redshx86/ro/fw/src/menu.h

// -------------------------------------------------------------------------------------------------

#pragma once

#include <stdint.h>

// -------------------------------------------------------------------------------------------------

void beep(uint8_t dur);

void menu_enable();
void menu_disable();

// -------------------------------------------------------------------------------------------------
